OrsoEric/OrangeBot-motor-controller-v2/Breadboard Firmware/src/at_utils.h

/****************************************************************************
**	R@P PROJECT
*****************************************************************************
**	AT_UTILS
**	Useful Atmel configuration macros
*****************************************************************************
**	Author: 			Orso Eric
**	Creation Date:		21/05/09
**	Last Edit Date:
**	Revision:			4
**	Version:			1.3
****************************************************************************/

/****************************************************************************
**	HYSTORY VERSION
*****************************************************************************
**	R1V1.0:
**		>implemented generic macro
**		>implemented port configuration macro
**		>implemented UART module macro
**	R2V1.1:
**		>added NOP macro
**		>added MASK macro
**		>added TOGGLE_BIT macro
**		>removed SET_2BIT macro (useless)
**		>removed SET_PORT_VALUE macro (useless)
**		>renamed SET_PORT macro to SET_VAR
**		>renamed CLEAR_PORT macro to CLEAR_VAR
**		>updated PORT_CONFIG macro
**		>updated USART macro handling
**		>added USART enviroment variablile to avoid those annoying warning
**		>comment updated
**		>code reformatted
**	R3V1.2
**		>Removed Shift Macro
**		>Removed Clear and SEt variabile macros
**		>Added conditional creation of PORT MACROS
**		>Added Saturated Math MACROS
**		>Added Fixed point MUL macros
**		>Added 8 bit Fixed point mul macros
**		>Added 8 bit fixed point rounded toward even mul macro
**		>Added 16 bit Fixed point mul macros
**		X>Added 16 bit fixed point rounded toward even mul macro
**	R4V1.3
**		>added circular buffer structure and handling macros
**		>added circular buffer with semaphor, allow for safe buffer push and kick
**		use in ISR and concurrent code
**		>added 8 bit exact logarithm macros
**		>added IS_NUMBR macro
**	2019-10-04
**		remove NULL. use nullptr
**	2019-10-13
**		SET_MASKED_BIT: set bit with external mask
**		SET_BIT_VALUE: set a bit to a desired true/false value
**	2019-11-10
**		TODO: update debug macros
**		BUG: AT_FP_SAT_MUL16 is bugged
**		2020-02-04
**	Debugged and tested
**	SHR, SHR_RTO, SSHR, SSHR_RTO
****************************************************************************/
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
